FanieVenter/VNTR-65/Images/Screenshot 2026-07-16 125014.png

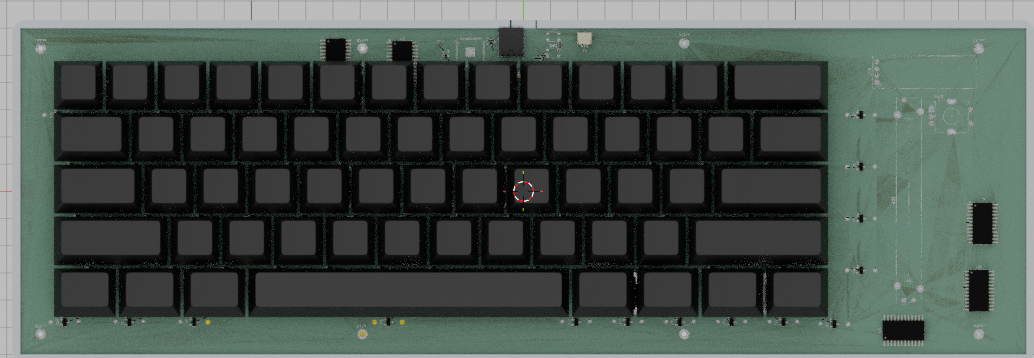
Images/Screenshot 2026-07-16 125014.png
