FanieVenter/VNTR-65/Images/silkscreen.png

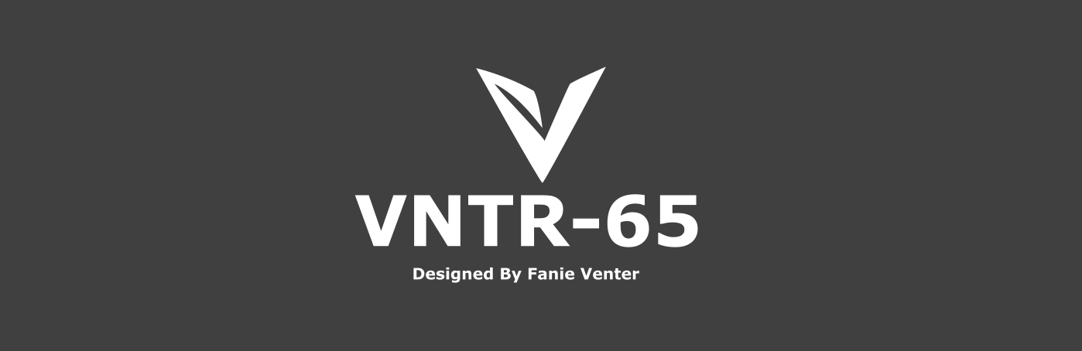
Images/silkscreen.png
