FanieVenter/VNTR-65/Hardware/PCB/Switches.kicad_sch

## KiCad design Hardware/PCB/Switches.kicad_sch (2026-07-17)

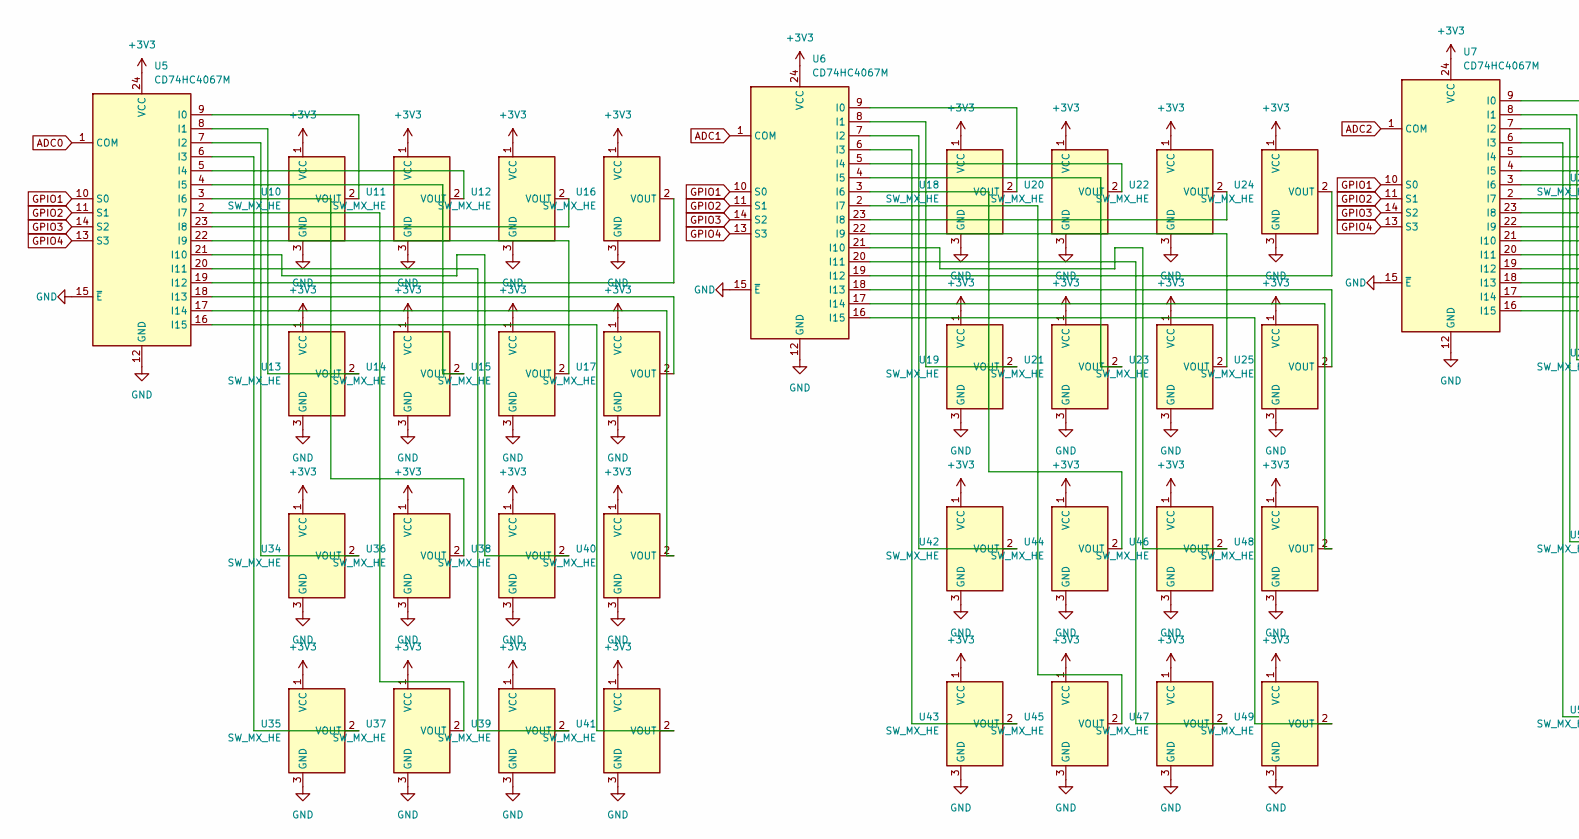
[picture p37: schematic Switches.kicad_sch, part in row 1, column 1]

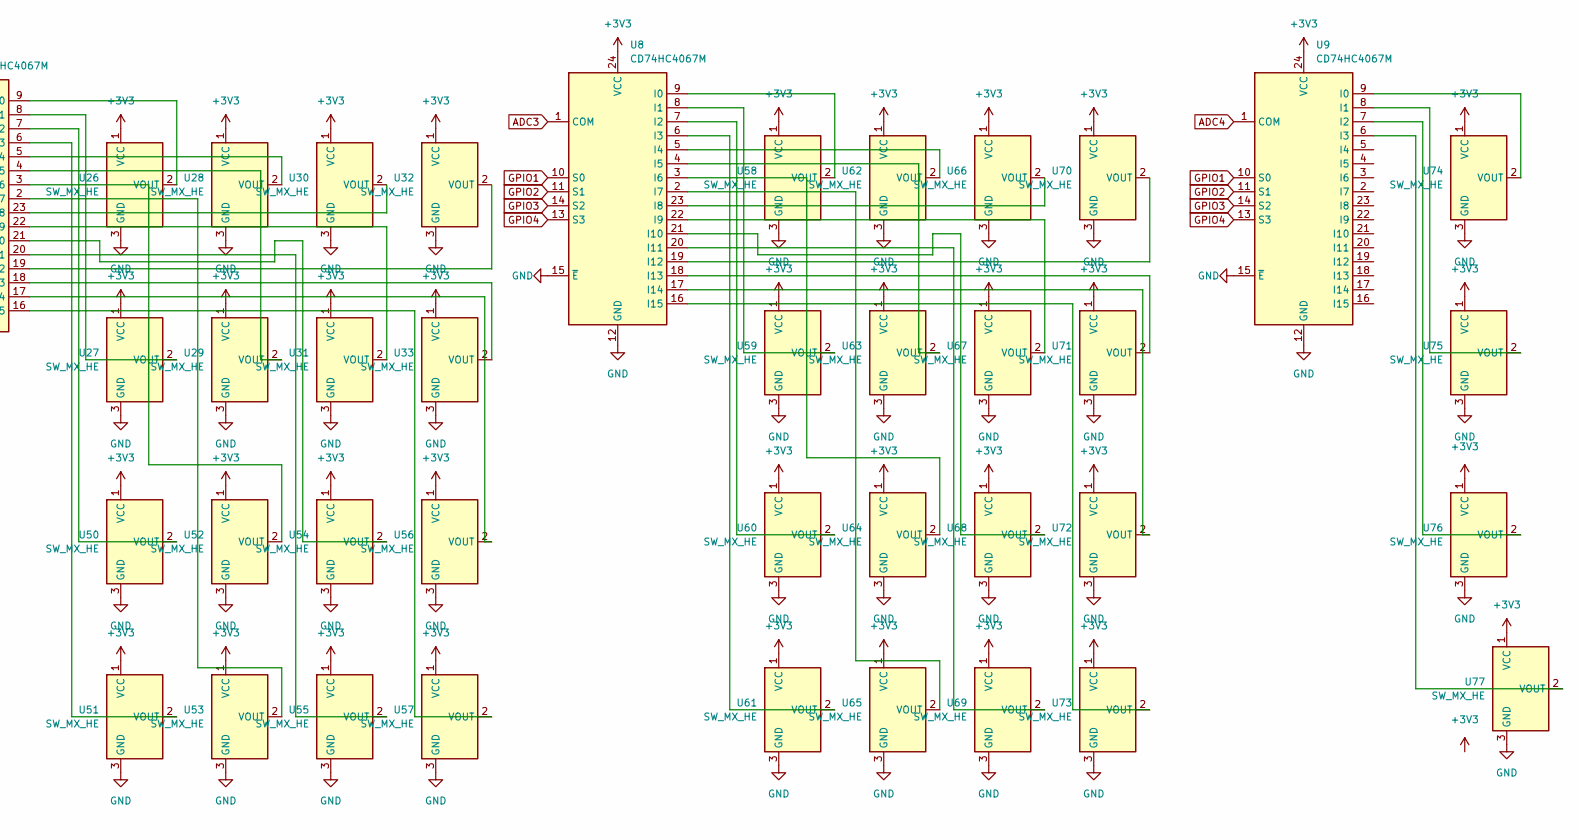
[picture p38: schematic Switches.kicad_sch, part in row 1, column 2]

Parts:
U5, U6, U7, U8, U9: CD74HC4067M; SOIC-24W_7.5x15.4mm_P1.27mm
U10, U11, U12, U13, U14, U15, U16, U17, U18, U19, U20, U21, U22, U23, U24, U25, U26, U27, U28, U29, U30, U31, U32, U33, U34, U35, U36, U37, U38, U39, U40, U41, U42, U43, U44, U45, U46, U47, U48, U49, U50, U51, U52, U53, U54, U55, U56, U57, U58, U59, U60, U61, U62, U63, U64, U65, U66, U67, U68, U69, U70, U71, U72, U73, U74, U75, U76, U77: SW_MX_HE; SW_MX_HE_0deg_1u

Connections:
+3V3: U5.24 (VCC), U6.24 (VCC), U7.24 (VCC), U8.24 (VCC), U9.24 (VCC), U10.1 (VCC), U11.1 (VCC), U12.1 (VCC), U13.1 (VCC), U14.1 (VCC), U15.1 (VCC), U16.1 (VCC), U17.1 (VCC), U18.1 (VCC), U19.1 (VCC), U20.1 (VCC), U21.1 (VCC), U22.1 (VCC), U23.1 (VCC), U24.1 (VCC), U25.1 (VCC), U26.1 (VCC), U27.1 (VCC), U28.1 (VCC), U29.1 (VCC), U30.1 (VCC), U31.1 (VCC), U32.1 (VCC), U33.1 (VCC), U34.1 (VCC), U35.1 (VCC), U36.1 (VCC), U37.1 (VCC), U38.1 (VCC), U39.1 (VCC), U40.1 (VCC), U41.1 (VCC), U42.1 (VCC), U43.1 (VCC), U44.1 (VCC), U45.1 (VCC), U46.1 (VCC), U47.1 (VCC), U48.1 (VCC), U49.1 (VCC), U50.1 (VCC), U51.1 (VCC), U52.1 (VCC), U53.1 (VCC), U54.1 (VCC), U55.1 (VCC), U56.1 (VCC), U57.1 (VCC), U58.1 (VCC), U59.1 (VCC), U60.1 (VCC), U61.1 (VCC), U62.1 (VCC), U63.1 (VCC), U64.1 (VCC), U65.1 (VCC), U66.1 (VCC), U67.1 (VCC), U68.1 (VCC), U69.1 (VCC), U70.1 (VCC), U71.1 (VCC), U72.1 (VCC), U73.1 (VCC), U74.1 (VCC), U75.1 (VCC), U76.1 (VCC), U77.1 (VCC)
ADC0: U5.1 (COM)
ADC1: U6.1 (COM)
ADC2: U7.1 (COM)
ADC3: U8.1 (COM)
ADC4: U9.1 (COM)
GND: U5.12 (GND), U5.15 (~E), U6.12 (GND), U6.15 (~E), U7.12 (GND), U7.15 (~E), U8.12 (GND), U8.15 (~E), U9.12 (GND), U9.15 (~E), U10.3 (GND), U11.3 (GND), U12.3 (GND), U13.3 (GND), U14.3 (GND), U15.3 (GND), U16.3 (GND), U17.3 (GND), U18.3 (GND), U19.3 (GND), U20.3 (GND), U21.3 (GND), U22.3 (GND), U23.3 (GND), U24.3 (GND), U25.3 (GND), U26.3 (GND), U27.3 (GND), U28.3 (GND), U29.3 (GND), U30.3 (GND), U31.3 (GND), U32.3 (GND), U33.3 (GND), U34.3 (GND), U35.3 (GND), U36.3 (GND), U37.3 (GND), U38.3 (GND), U39.3 (GND), U40.3 (GND), U41.3 (GND), U42.3 (GND), U43.3 (GND), U44.3 (GND), U45.3 (GND), U46.3 (GND), U47.3 (GND), U48.3 (GND), U49.3 (GND), U50.3 (GND), U51.3 (GND), U52.3 (GND), U53.3 (GND), U54.3 (GND), U55.3 (GND), U56.3 (GND), U57.3 (GND), U58.3 (GND), U59.3 (GND), U60.3 (GND), U61.3 (GND), U62.3 (GND), U63.3 (GND), U64.3 (GND), U65.3 (GND), U66.3 (GND), U67.3 (GND), U68.3 (GND), U69.3 (GND), U70.3 (GND), U71.3 (GND), U72.3 (GND), U73.3 (GND), U74.3 (GND), U75.3 (GND), U76.3 (GND), U77.3 (GND)
GPIO1: U5.10 (S0), U6.10 (S0), U7.10 (S0), U8.10 (S0), U9.10 (S0)
GPIO2: U5.11 (S1), U6.11 (S1), U7.11 (S1), U8.11 (S1), U9.11 (S1)
GPIO3: U5.14 (S2), U6.14 (S2), U7.14 (S2), U8.14 (S2), U9.14 (S2)
GPIO4: U5.13 (S3), U6.13 (S3), U7.13 (S3), U8.13 (S3), U9.13 (S3)
unnamed: U5.9 (I0), U10.2 (VOUT)
unnamed: U5.5 (I4), U11.2 (VOUT)
unnamed: U5.23 (I8), U12.2 (VOUT)
unnamed: U5.8 (I1), U13.2 (VOUT)
unnamed: U5.4 (I5), U14.2 (VOUT)
unnamed: U5.22 (I9), U15.2 (VOUT)
unnamed: U5.19 (I12), U16.2 (VOUT)
unnamed: U5.18 (I13), U17.2 (VOUT)
unnamed: U6.9 (I0), U18.2 (VOUT)
unnamed: U6.8 (I1), U19.2 (VOUT)
unnamed: U6.5 (I4), U20.2 (VOUT)
unnamed: U6.4 (I5), U21.2 (VOUT)
unnamed: U6.23 (I8), U22.2 (VOUT)
unnamed: U6.22 (I9), U23.2 (VOUT)
unnamed: U6.19 (I12), U24.2 (VOUT)
unnamed: U6.18 (I13), U25.2 (VOUT)
unnamed: U7.9 (I0), U26.2 (VOUT)
unnamed: U7.8 (I1), U27.2 (VOUT)
unnamed: U7.5 (I4), U28.2 (VOUT)
unnamed: U7.4 (I5), U29.2 (VOUT)
unnamed: U7.23 (I8), U30.2 (VOUT)
unnamed: U7.22 (I9), U31.2 (VOUT)
unnamed: U7.19 (I12), U32.2 (VOUT)
unnamed: U7.18 (I13), U33.2 (VOUT)
unnamed: U5.7 (I2), U34.2 (VOUT)
unnamed: U5.6 (I3), U35.2 (VOUT)
unnamed: U5.3 (I6), U36.2 (VOUT)
unnamed: U5.2 (I7), U37.2 (VOUT)
unnamed: U5.21 (I10), U38.2 (VOUT)
unnamed: U5.20 (I11), U39.2 (VOUT)
unnamed: U5.17 (I14), U40.2 (VOUT)
unnamed: U5.16 (I15), U41.2 (VOUT)
unnamed: U6.7 (I2), U42.2 (VOUT)
unnamed: U6.6 (I3), U43.2 (VOUT)
unnamed: U6.3 (I6), U44.2 (VOUT)
unnamed: U6.2 (I7), U45.2 (VOUT)
unnamed: U6.21 (I10), U46.2 (VOUT)
unnamed: U6.20 (I11), U47.2 (VOUT)
unnamed: U6.17 (I14), U48.2 (VOUT)
unnamed: U6.16 (I15), U49.2 (VOUT)
unnamed: U7.7 (I2), U50.2 (VOUT)
unnamed: U7.6 (I3), U51.2 (VOUT)
unnamed: U7.3 (I6), U52.2 (VOUT)
unnamed: U7.2 (I7), U53.2 (VOUT)
unnamed: U7.21 (I10), U54.2 (VOUT)
unnamed: U7.20 (I11), U55.2 (VOUT)
unnamed: U7.17 (I14), U56.2 (VOUT)
unnamed: U7.16 (I15), U57.2 (VOUT)
unnamed: U8.9 (I0), U58.2 (VOUT)
unnamed: U8.8 (I1), U59.2 (VOUT)
unnamed: U8.7 (I2), U60.2 (VOUT)
unnamed: U8.6 (I3), U61.2 (VOUT)
unnamed: U8.5 (I4), U62.2 (VOUT)
unnamed: U8.4 (I5), U63.2 (VOUT)
unnamed: U8.3 (I6), U64.2 (VOUT)
unnamed: U8.2 (I7), U65.2 (VOUT)
unnamed: U8.23 (I8), U66.2 (VOUT)
unnamed: U8.22 (I9), U67.2 (VOUT)
unnamed: U8.21 (I10), U68.2 (VOUT)
unnamed: U8.20 (I11), U69.2 (VOUT)
unnamed: U8.19 (I12), U70.2 (VOUT)
unnamed: U8.18 (I13), U71.2 (VOUT)
unnamed: U8.17 (I14), U72.2 (VOUT)
unnamed: U8.16 (I15), U73.2 (VOUT)
unnamed: U9.9 (I0), U74.2 (VOUT)
unnamed: U9.8 (I1), U75.2 (VOUT)
unnamed: U9.7 (I2), U76.2 (VOUT)
unnamed: U9.6 (I3), U77.2 (VOUT)
