FanieVenter/VNTR-65/Hardware/PCB/VNTR-65.kicad_sch

## KiCad design Hardware/PCB/VNTR-65.kicad_sch (2026-09-05)

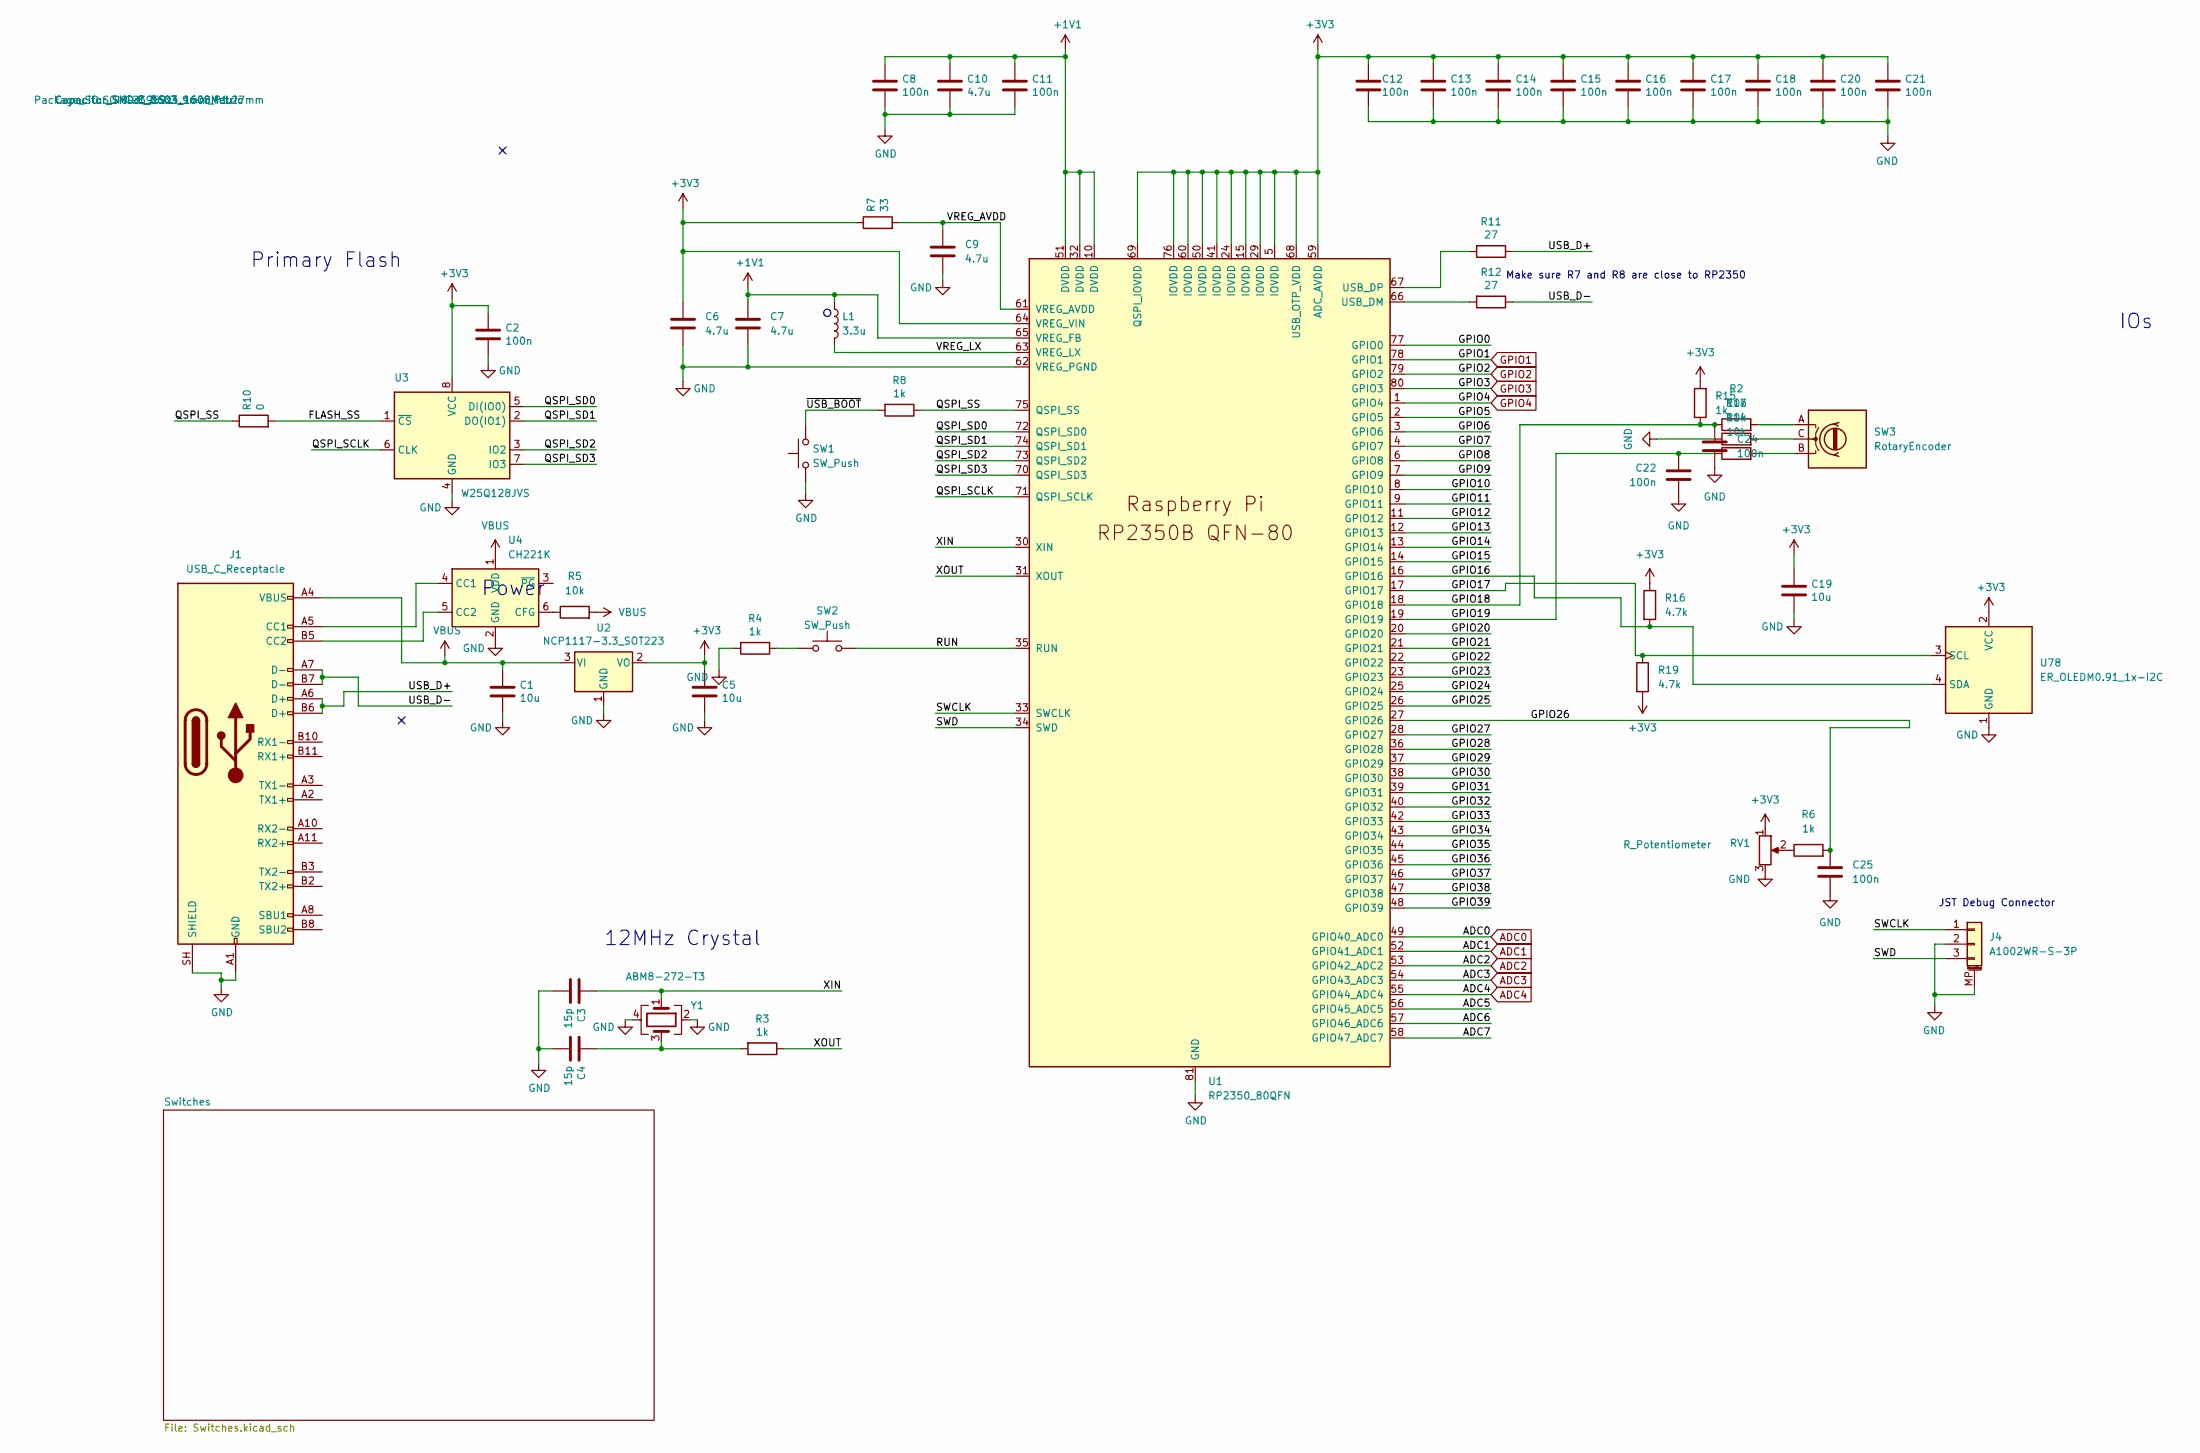
[picture p39: schematic VNTR-65.kicad_sch]

Parts:
C1, C5, C19: 10u; C_0603_1608Metric
C2, C8, C11, C12, C13, C14, C15, C16, C17, C18, C20, C21, C22, C24, C25: 100n; C_0603_1608Metric
C3, C4: 15p; C_0603_1608Metric
C6, C7, C9, C10: 4.7u; C_0603_1608Metric
J1: USB_C_Receptacle; USB_C_Receptacle_Amphenol_12401610E4-2A
J4: A1002WR-S-3P; JST_SH_SM03B-SRSS-TB_1x03-1MP_P1.00mm_Horizontal; LCSC Part # C239521
L1: 3.3u; L_pol_2016
R2, R5, R13, R14: 10k; R_0603_1608Metric
R3, R4, R6, R8, R15: 1k; R_0603_1608Metric
R7: 33; R_0603_1608Metric
R10: 0; R_0603_1608Metric
R11, R12: 27; R_0603_1608Metric
R16, R19: 4.7k; R_0603_1608Metric
RV1: R_Potentiometer; Potentiometer_Bourns_PTA6043_Single_Slide
SW1, SW2: SW_Push; SW_Push_1P1T_NO_Vertical_Wuerth_434133025816
SW3: RotaryEncoder; RotaryEncoder_Alps_EC11E-Switch_Vertical_H20mm
U1: RP2350_80QFN; QFN-80-1EP_10x10mm_P0.4mm_EP3.4x3.4mm
U2: NCP1117-3.3_SOT223; SOT-223-3_TabPin2
U3: W25Q128JVS; SOIC-8_3.9x4.9mm_P1.27mm
U4: CH221K; SOT-23-6
U78: ER_OLEDM0.91_1x-I2C
Y1: ABM8-272-T3; Crystal_SMD_3225-4Pin_3.2x2.5mm

Connections:
+1V1: C7.1, C8.1, C10.1, C11.1, L1.1, U1.10 (DVDD), U1.32 (DVDD), U1.51 (DVDD), U1.65 (VREG_FB)
+3V3: C2.1, C5.1, C6.1, C12.1, C13.1, C14.1, C15.1, C16.1, C17.1, C18.1, C19.1, C20.1, C21.1, R7.1, R15.2, R16.1, R19.2, RV1.1, U1.5 (IOVDD), U1.15 (IOVDD), U1.24 (IOVDD), U1.29 (IOVDD), U1.41 (IOVDD), U1.50 (IOVDD), U1.59 (ADC_AVDD), U1.60 (IOVDD), U1.64 (VREG_VIN), U1.68 (USB_OTP_VDD), U1.69 (QSPI_IOVDD), U1.76 (IOVDD), U2.2 (VO), U3.8 (VCC), U78.2 (VCC)
ADC0: U1.49 (GPIO40_ADC0)
ADC1: U1.52 (GPIO41_ADC1)
ADC2: U1.53 (GPIO42_ADC2)
ADC3: U1.54 (GPIO43_ADC3)
ADC4: U1.55 (GPIO44_ADC4)
ADC5: U1.56 (GPIO45_ADC5)
ADC6: U1.57 (GPIO46_ADC6)
ADC7: U1.58 (GPIO47_ADC7)
FLASH_SS: R10.2, U3.1 (~CS)
GND: C1.2, C2.2, C3.2, C4.2, C5.2, C6.2, C7.2, C8.2, C9.2, C10.2, C11.2, C12.2, C13.2, C14.2, C15.2, C16.2, C17.2, C18.2, C19.2, C20.2, C21.2, C22.1, C24.1, C25.1, J1.A1 (GND), J1.A12 (GND), J1.B1 (GND), J1.B12 (GND), J1.SH (SHIELD), J4.2, J4.MP (MountPin), R4.2, R13.1, RV1.3, SW1.1, U1.62 (VREG_PGND), U1.81 (GND), U2.1 (GND), U3.4 (GND), U4.2 (GND), U78.1 (GND), Y1.2, Y1.4
GPIO0: U1.77 (GPIO0)
GPIO1: U1.78 (GPIO1)
GPIO2: U1.79 (GPIO2)
GPIO3: U1.80 (GPIO3)
GPIO4: U1.1 (GPIO4)
GPIO5: U1.2 (GPIO5)
GPIO6: U1.3 (GPIO6)
GPIO7: U1.4 (GPIO7)
GPIO8: U1.6 (GPIO8)
GPIO9: U1.7 (GPIO9)
GPIO10: U1.8 (GPIO10)
GPIO11: U1.9 (GPIO11)
GPIO12: U1.11 (GPIO12)
GPIO13: U1.12 (GPIO13)
GPIO14: U1.13 (GPIO14)
GPIO15: U1.14 (GPIO15)
GPIO16: R16.2, U1.16 (GPIO16), U78.4 (SDA)
GPIO17: R19.1, U1.17 (GPIO17), U78.3 (SCL)
GPIO18: C24.2, R2.1, R15.1, U1.18 (GPIO18)
GPIO19: C22.2, R14.1, U1.19 (GPIO19)
GPIO20: U1.20 (GPIO20)
GPIO21: U1.21 (GPIO21)
GPIO22: U1.22 (GPIO22)
GPIO23: U1.23 (GPIO23)
GPIO24: U1.25 (GPIO24)
GPIO25: U1.26 (GPIO25)
GPIO26: C25.2, R6.2, U1.27 (GPIO26)
GPIO27: U1.28 (GPIO27)
GPIO28: U1.36 (GPIO28)
GPIO29: U1.37 (GPIO29)
GPIO30: U1.38 (GPIO30)
GPIO31: U1.39 (GPIO31)
GPIO32: U1.40 (GPIO32)
GPIO33: U1.42 (GPIO33)
GPIO34: U1.43 (GPIO34)
GPIO35: U1.44 (GPIO35)
GPIO36: U1.45 (GPIO36)
GPIO37: U1.46 (GPIO37)
GPIO38: U1.47 (GPIO38)
GPIO39: U1.48 (GPIO39)
unnamed: C4.1, R3.2, Y1.3
unnamed: J1.A5 (CC1), U4.4 (CC1)
unnamed: J1.B5 (CC2), U4.5 (CC2)
unnamed: R2.2, SW3.A
unnamed: R4.1, SW2.1
unnamed: R5.1, U4.6 (CFG)
unnamed: R6.1, RV1.2
unnamed: R11.2, U1.67 (USB_DP)
unnamed: R12.2, U1.66 (USB_DM)
unnamed: R13.2, SW3.C
unnamed: R14.2, SW3.B
QSPI_SCLK: U1.71 (QSPI_SCLK), U3.6 (CLK)
QSPI_SD0: U1.72 (QSPI_SD0), U3.5 (DI(IO0))
QSPI_SD1: U1.74 (QSPI_SD1), U3.2 (DO(IO1))
QSPI_SD2: U1.73 (QSPI_SD2), U3.3 (IO2)
QSPI_SD3: U1.70 (QSPI_SD3), U3.7 (IO3)
QSPI_SS: R8.1, R10.1, U1.75 (QSPI_SS)
RUN: SW2.2, U1.35 (RUN)
SWCLK: J4.1, U1.33 (SWCLK)
SWD: J4.3, U1.34 (SWD)
USB_D+: J1.A6 (D+), J1.B6 (D+), R11.1
USB_D-: J1.A7 (D-), J1.B7 (D-), R12.1
VBUS: C1.1, J1.A4 (VBUS), J1.A9 (VBUS), J1.B4 (VBUS), J1.B9 (VBUS), R5.2, U2.3 (VI), U4.1 (VDD)
VREG_AVDD: C9.1, R7.2, U1.61 (VREG_AVDD)
VREG_LX: L1.2, U1.63 (VREG_LX)
XIN: C3.1, U1.30 (XIN), Y1.1
XOUT: R3.1, U1.31 (XOUT)
~USB_BOOT: R8.2, SW1.2

Notes on the sheet:
Make sure R7 and R8 are close to RP2350
JST Debug Connector
Power
12MHz Crystal
IOs
Primary Flash
